dlepaux/hexrack-sbc/cad/sections/body/fan.scad

include <../../config.scad>
use <../../lib/shapes.scad>
use <../../components/fan.scad>
use <../../components/drawers.scad>
use <../../components/mounting-holes.scad>

use <../../SBC_Model_Framework/sbc_models.scad>
include <../../SBC_Model_Framework/sbc_models.cfg>

use <../../lib/sbc-helpers.scad>
use <../../lib/pironman-base.scad>

module sectionFan() {
  body_height = hex_flat_to_flat(body_width);

  difference() {
    union() {
      translate([0, 0, (-body_width + body_height)/2])
      honeycomb_shell(body_width, fan_depth, 2.6);

      // Male
      honeycombLipMale();

      translate([0, fan_depth - 3, 0])
      intersection() {
        translate([0, 0, (-body_width + body_height)/2])
        honeycomb_box(body_width, 3, 0);

        translate([0, 0, (-body_width + body_height)/2])
        roundedPanel(
          body_width,
          wall_thickness,
          corner_radius,
          0,
          center_hole=fan_size_mode
        );
      }
    }

    // Female
    honeycombLipFemale(fan_depth);

    translate([0, -OVERLAP*5, 0])
    frontfaceMountingHolesFront(type="through", body_height=body_height);

    #translate([0, 0, (-body_width + body_height)/2])
    rotate([0, 0, 180])
    translate([-body_width, -fan_depth, 0])
    fanMountingHoles();

    // Cable exits for the fan, one per corner so any of its four rotations works.
    // Cut only into the 3mm web above -- at this radius the section is hollow, so
    // nothing else is in the way. See config.scad for the placement reasoning.
    if (enable_fan_wire_slots)
      translate([0, fan_depth - 3, (-body_width + body_height)/2])
      fanWireSlots(
        size = body_width,
        thickness = 3,
        bore = fan_size_mode,
        screw_offset = fan_screw_offset(fan_size_mode),
        radius = fan_wire_slot_radius,
        reach = fan_wire_slot_reach,
        angle = fan_wire_slot_angle,
        clearance = fan_wire_slot_clearance,
        chamfer = fan_wire_slot_chamfer
      );
  }

  if (show_fan) {
    %translate([body_width/2, fan_depth, body_height/2])
    fanVisualization92();
  }
}
